alibabaABC/arduino-lelo-remote/vibeam02/RunningMedian.h

#ifndef RunningMedian_h
#define RunningMedian_h
// 
//    FILE: RunningMedian.h
//  AUTHOR: Rob dot Tillaart at gmail dot com  
// PURPOSE: RunningMedian library for Arduino
// VERSION: 0.2.00 - template edition
//     URL: http://arduino.cc/playground/Main/RunningMedian
// HISTORY: 0.2.00 first template version by Ronny
//
// Released to the public domain
//


template <typename T, int N> class RunningMedian {

public:

	enum STATUS {OK = 0, NOK = 1};

	RunningMedian() {
		_size = N;
		clear();
	};

	void clear() {
		_cnt = 0;
		_idx = 0;
	};

	void add(T value) {
		_ar[_idx++] = value;
		if (_idx >= _size) _idx = 0; // wrap around
		if (_cnt < _size) _cnt++;
	};

	STATUS getMedian(T& value) {
		if (_cnt > 0) {
			sort();
			value = _as[_cnt/2];
			return OK;
		}
		return NOK;
	};

	STATUS getAverage(float &value) {
		if (_cnt > 0) {
			float sum = 0;
			for (uint8_t i=0; i< _cnt; i++) sum += _ar[i];
			value = sum / _cnt;
			return OK;
		}
		return NOK;
	};

	STATUS getHighest(T& value) {
		if (_cnt > 0) {
			sort();
			value = _as[_cnt-1];
			return OK;
		}
		return NOK;
	};

	STATUS getLowest(T& value) {
		if (_cnt > 0) {
			sort();
			value =  _as[0];
			return OK;
		}
		return NOK;
	};

	unsigned getSize() {
		return _size;
	};

	unsigned getCount() {
		return _cnt;
	}

	STATUS getStatus() {
		return (_cnt > 0 ? OK : NOK);
	};

private:
	uint8_t _size;
	uint8_t _cnt;
	uint8_t _idx;
	T _ar[N];
	T _as[N];
	void sort() {
		// copy
		for (uint8_t i=0; i< _cnt; i++) _as[i] = _ar[i];

		// sort all
		for (uint8_t i=0; i< _cnt-1; i++) {
			uint8_t m = i;
			for (uint8_t j=i+1; j< _cnt; j++) {
				if (_as[j] < _as[m]) m = j;
			}
			if (m != i) {
				T t = _as[m];
				_as[m] = _as[i];
				_as[i] = t;
			}
		}
	};
};

#endif
// --- END OF FILE ---
